mplanton/vierfach_LFO/pic/IMG_20220212_112719_1.jpg

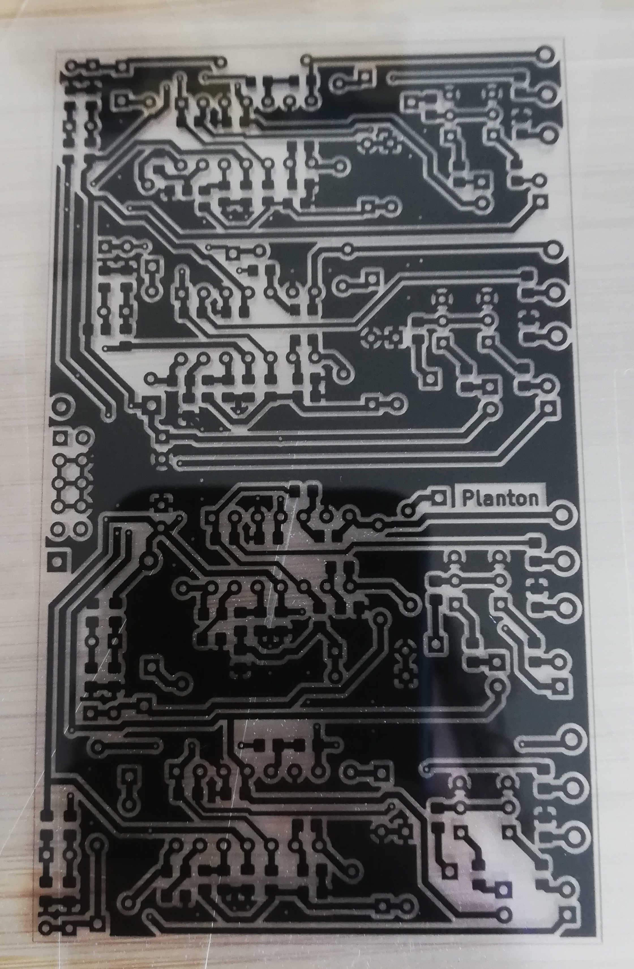
pic/IMG_20220212_112719_1.jpg
