mplanton/vierfach_LFO/pic/IMG_20220212_123942_1.jpg

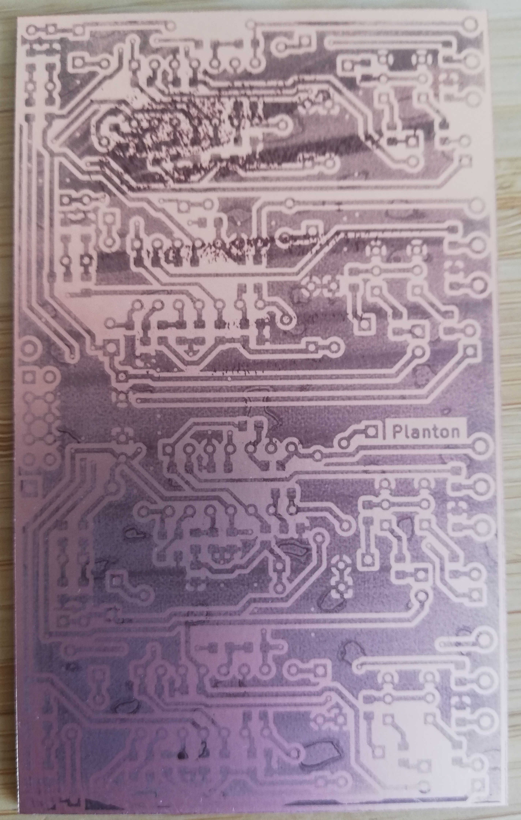
pic/IMG_20220212_123942_1.jpg
