mplanton/vierfach_LFO/pic/IMG_20220212_140111_1.jpg

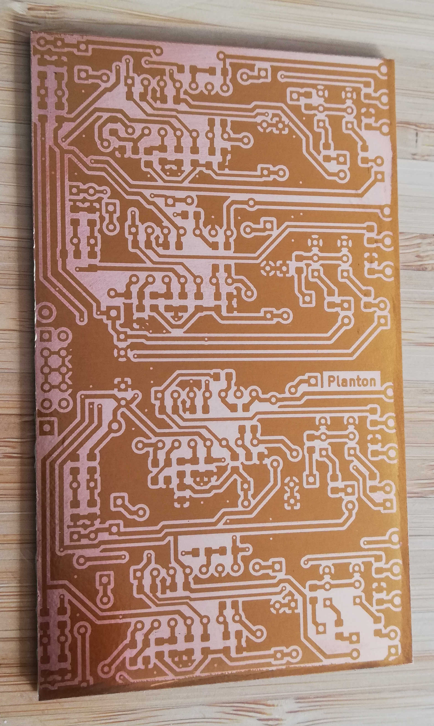
pic/IMG_20220212_140111_1.jpg
