mplanton/vierfach_LFO/pic/IMG_20220212_180620_1.jpg

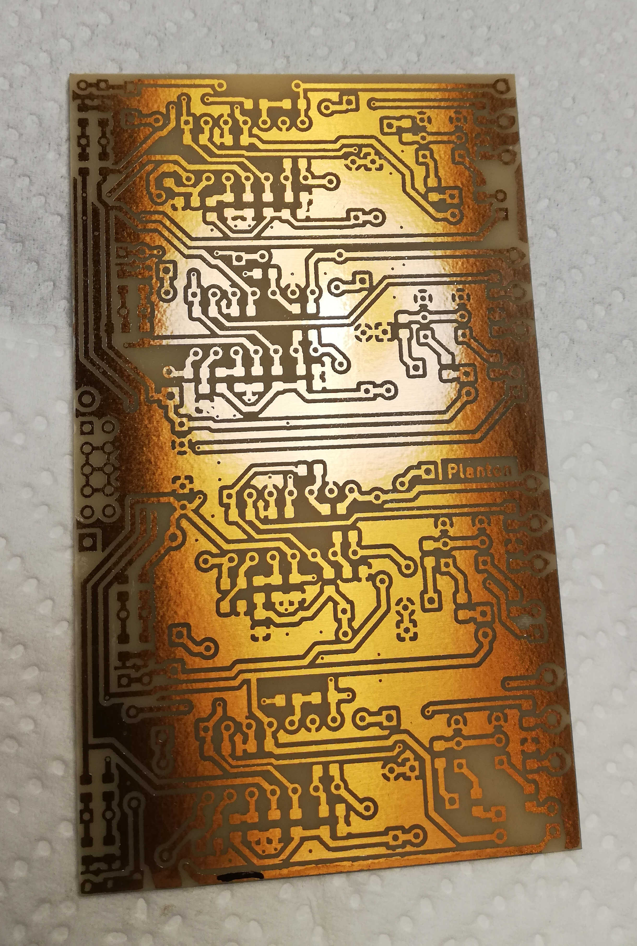
pic/IMG_20220212_180620_1.jpg
