mplanton/vierfach_LFO/pic/IMG_20220216_200657_1.jpg

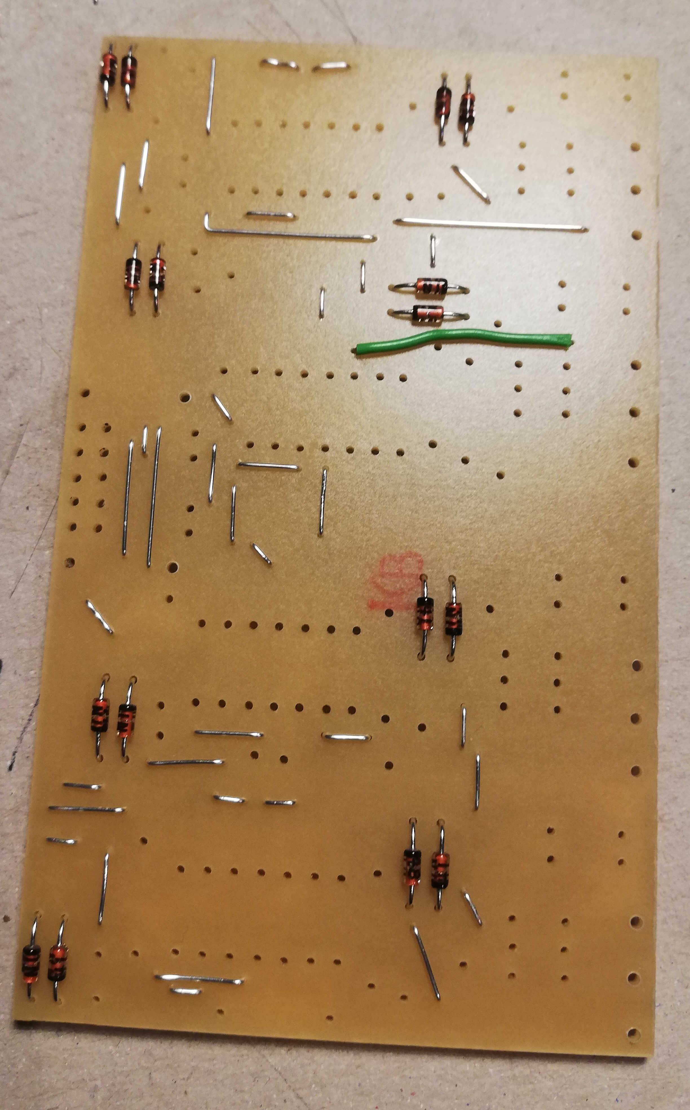
pic/IMG_20220216_200657_1.jpg
