mplanton/vierfach_LFO/pic/IMG_20220217_171207_1.jpg

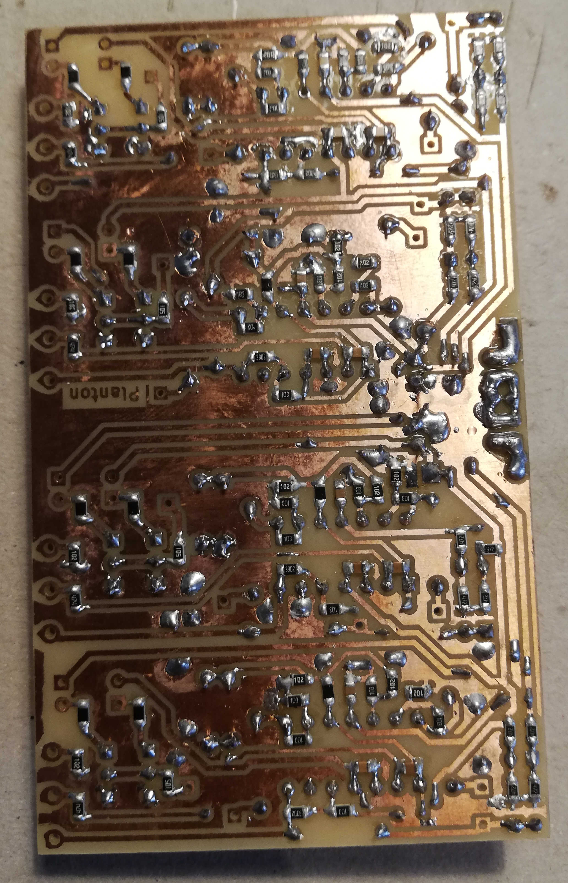
pic/IMG_20220217_171207_1.jpg
