mplanton/vierfach_LFO/pic/IMG_20220217_171452_1.jpg

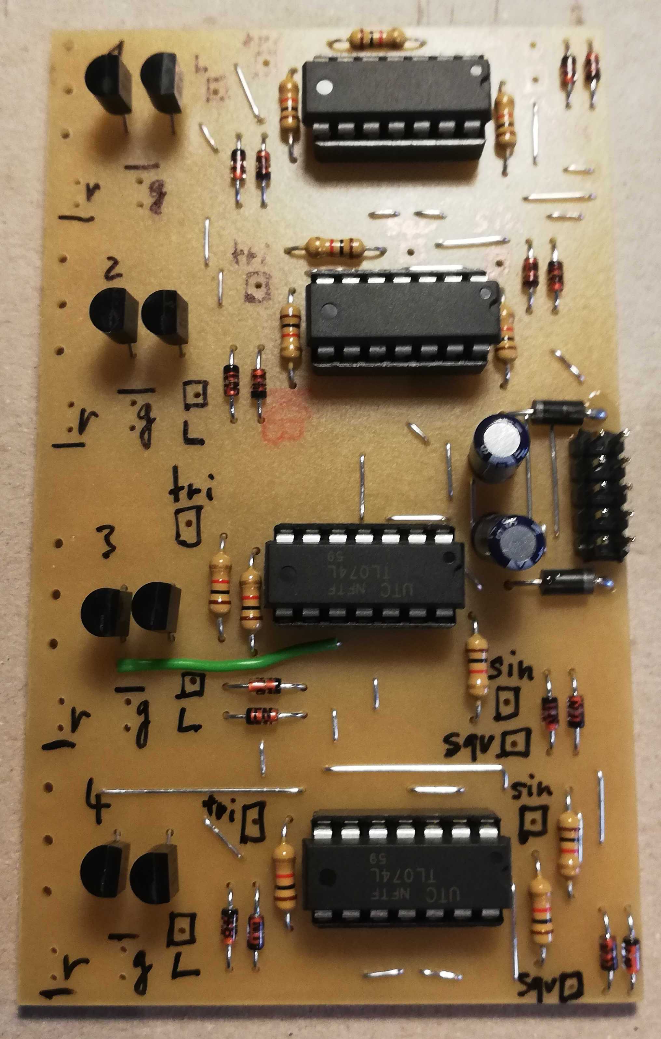
pic/IMG_20220217_171452_1.jpg
