mplanton/vierfach_LFO/pic/IMG_20220217_223229_1.jpg

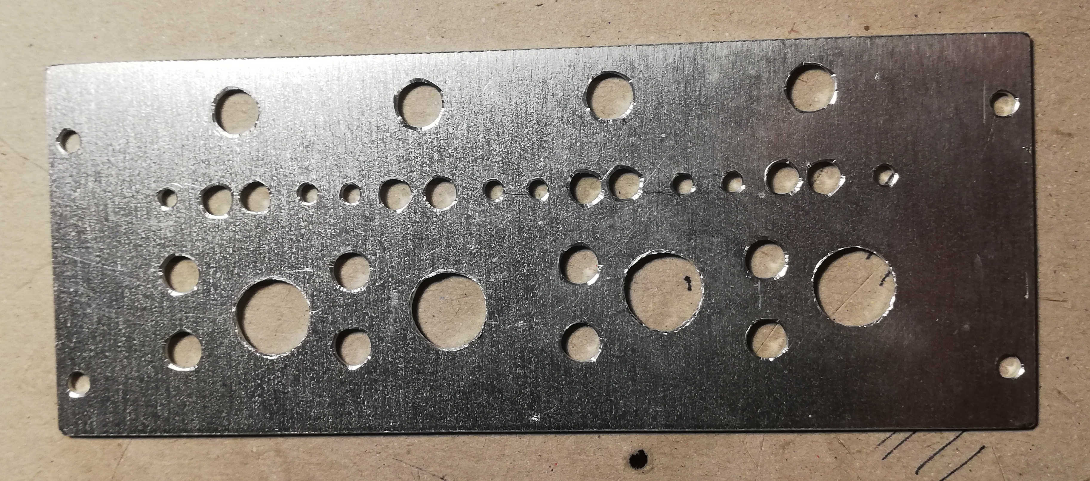
pic/IMG_20220217_223229_1.jpg
