mplanton/vierfach_LFO/pic/IMG_20220218_182223_1.jpg

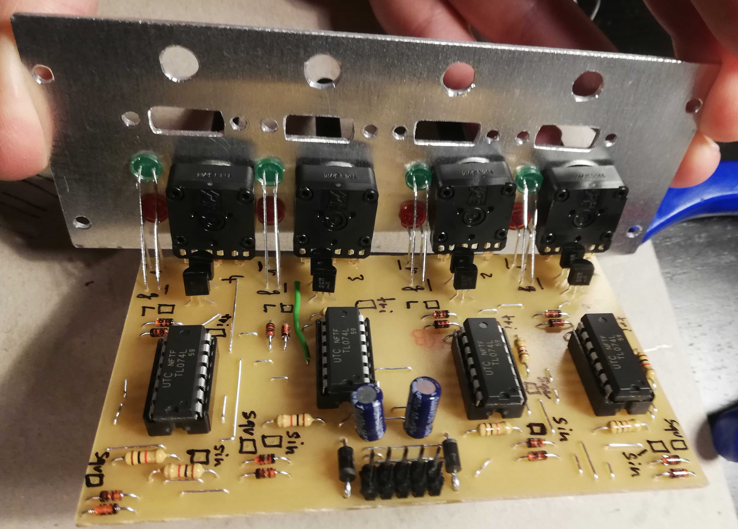
pic/IMG_20220218_182223_1.jpg
