mplanton/vierfach_LFO/pic/IMG_20220218_183138_1.jpg

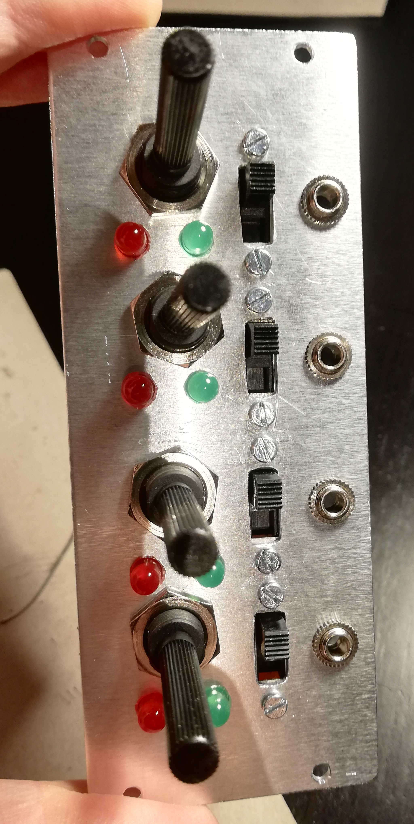
pic/IMG_20220218_183138_1.jpg
