mplanton/vierfach_LFO/pic/IMG_20220218_211930_1.jpg

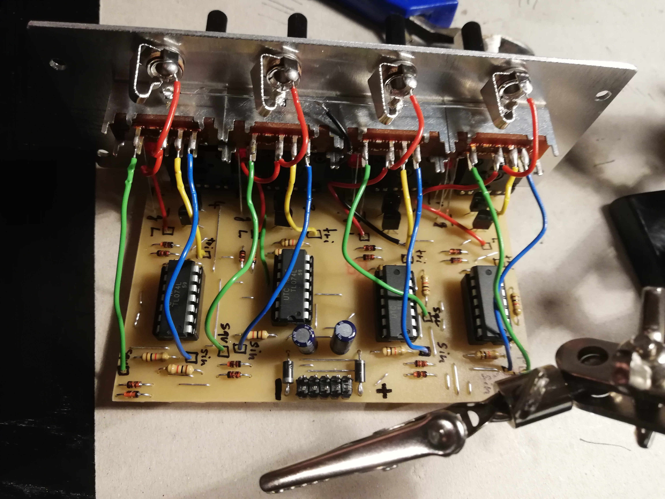
pic/IMG_20220218_211930_1.jpg
