mplanton/vierfach_LFO/pic/IMG_20220218_212823_1.jpg

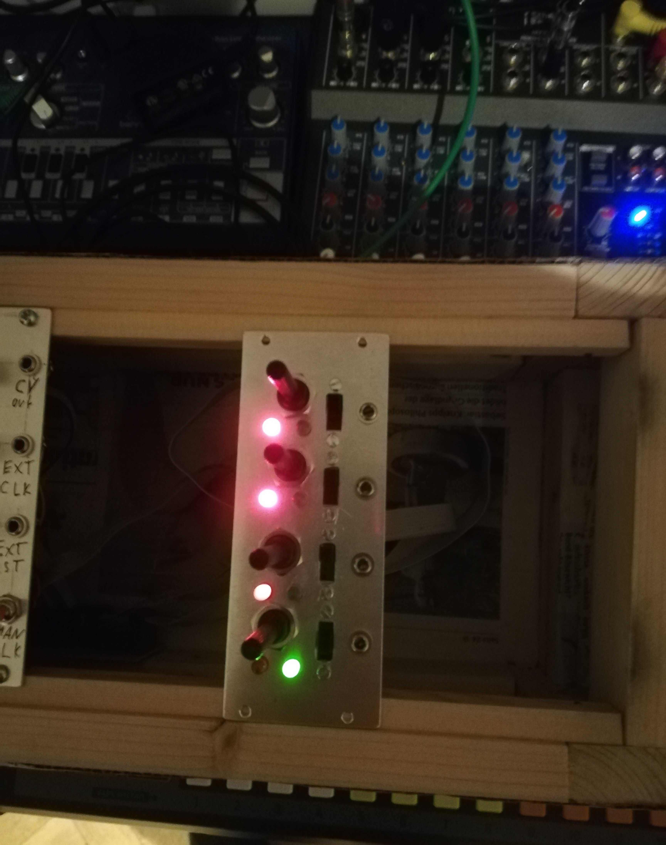
pic/IMG_20220218_212823_1.jpg
